JozefWR/Automat-Do-Dozowania-Plyn-w-ESP32/plytka_sterownika/2.png

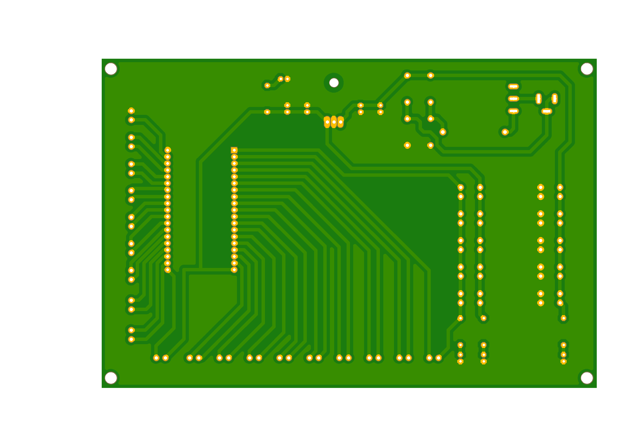
plytka_sterownika/2.png
